hashedslasher/kaiju-ndt/plots/9-2-26/plot_20260902_162636.png

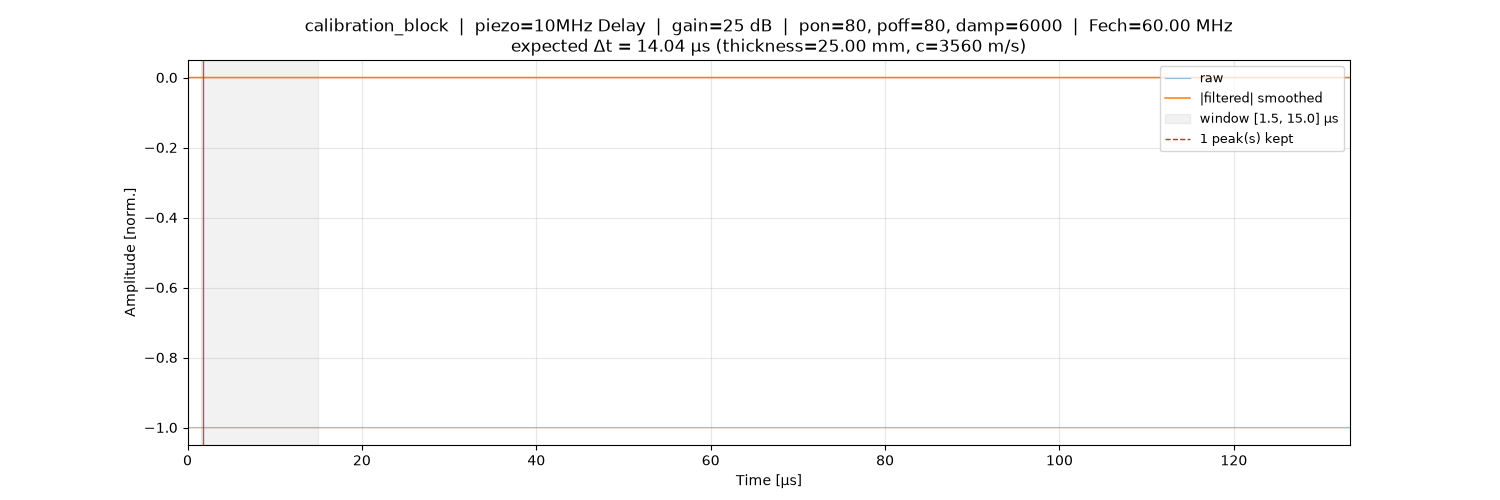
plots/9-2-26/plot_20260902_162636.png
