hashedslasher/kaiju-ndt/plots/9-3-26/plot_20260903_183738.png

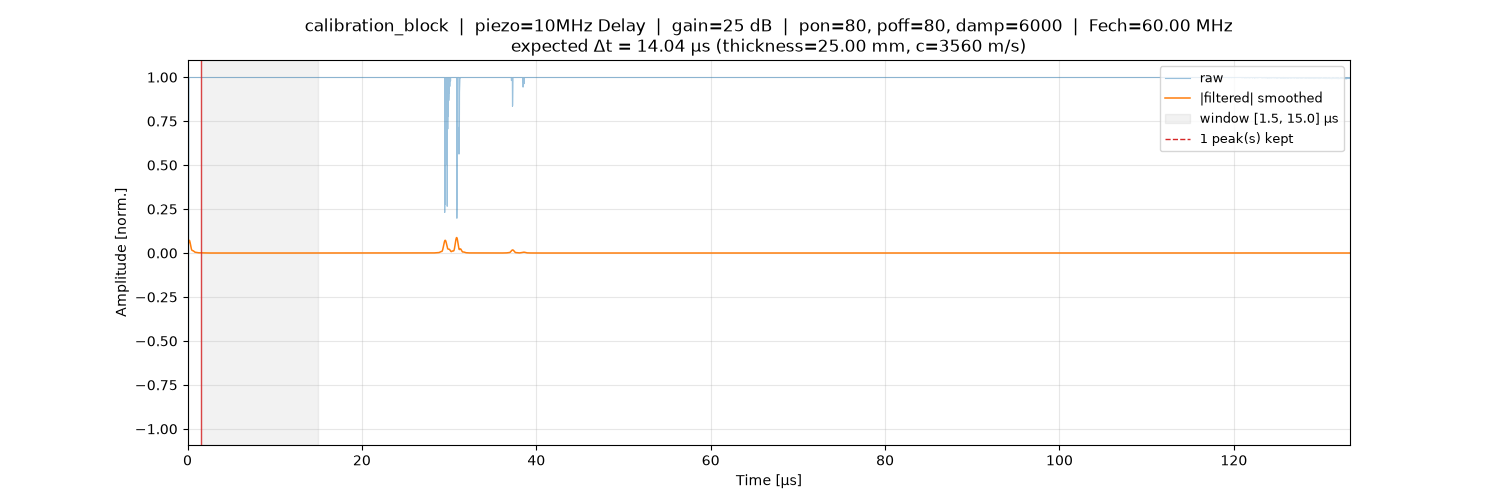
plots/9-3-26/plot_20260903_183738.png
