hashedslasher/kaiju-ndt/plots/9-3-26/plot_20260903_190933.png

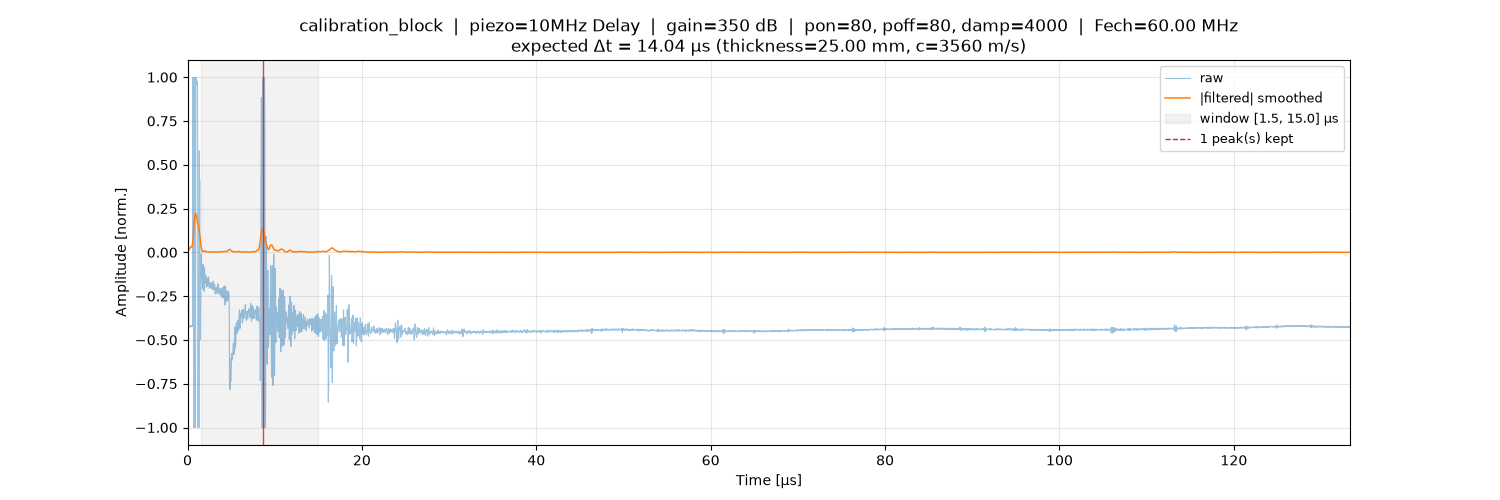
plots/9-3-26/plot_20260903_190933.png
