hashedslasher/kaiju-ndt/plots/9-3-26/plot_20260903_191829.png

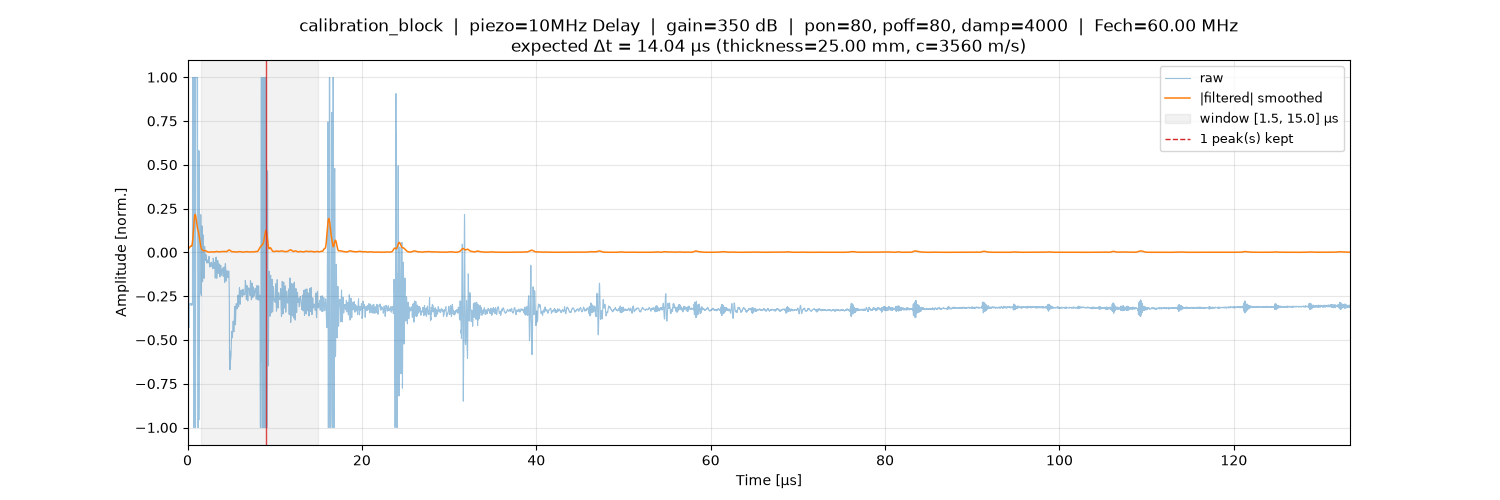
plots/9-3-26/plot_20260903_191829.png
