hashedslasher/kaiju-ndt/plots/9-3-26/plot_20260903_192204.png

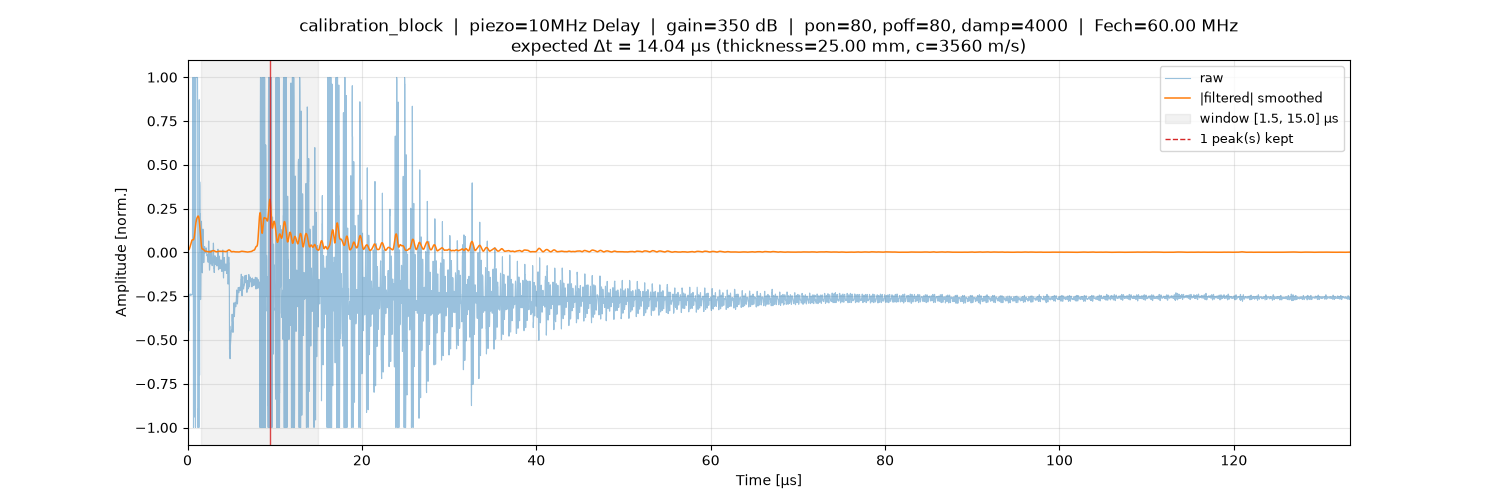
plots/9-3-26/plot_20260903_192204.png
