hashedslasher/kaiju-ndt/plots/9-4-26/plot_20260904_101053.png

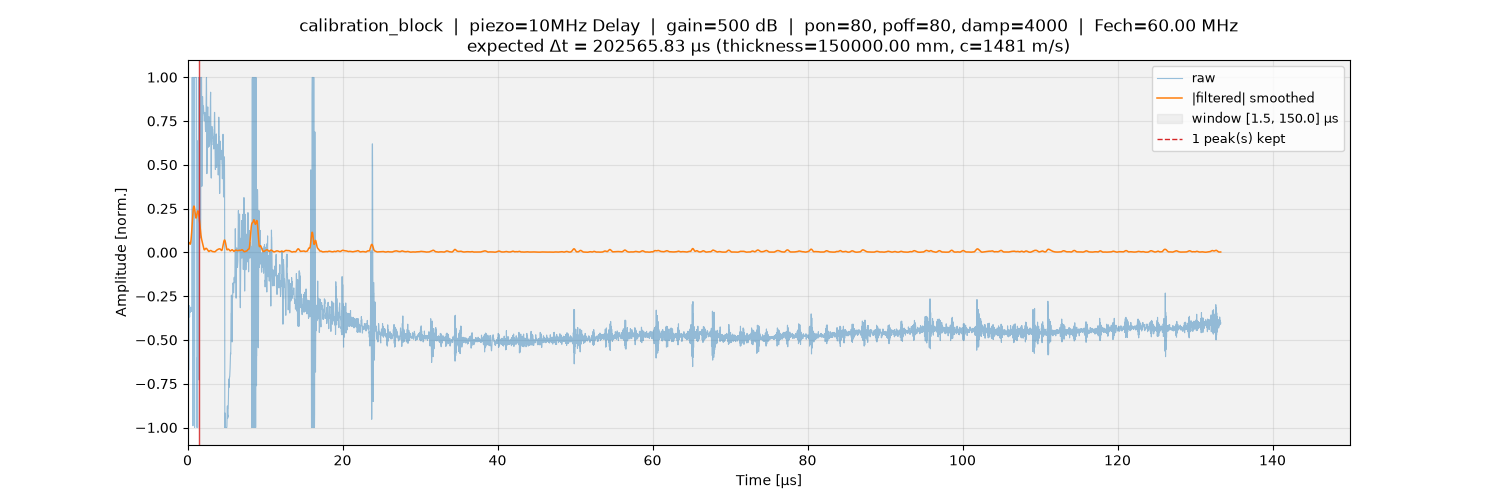
plots/9-4-26/plot_20260904_101053.png
