hashedslasher/kaiju-ndt/plots/9-4-26/plot_20260904_101120.png

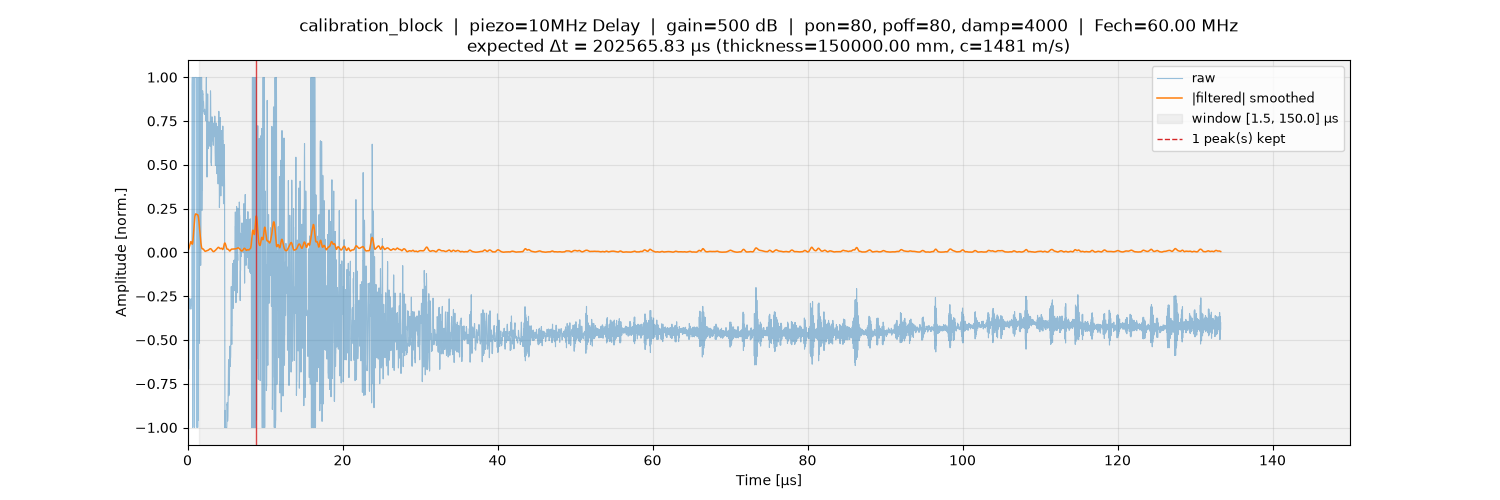
plots/9-4-26/plot_20260904_101120.png
