hashedslasher/kaiju-ndt/plots/9-4-26/plot_20260904_101206.png

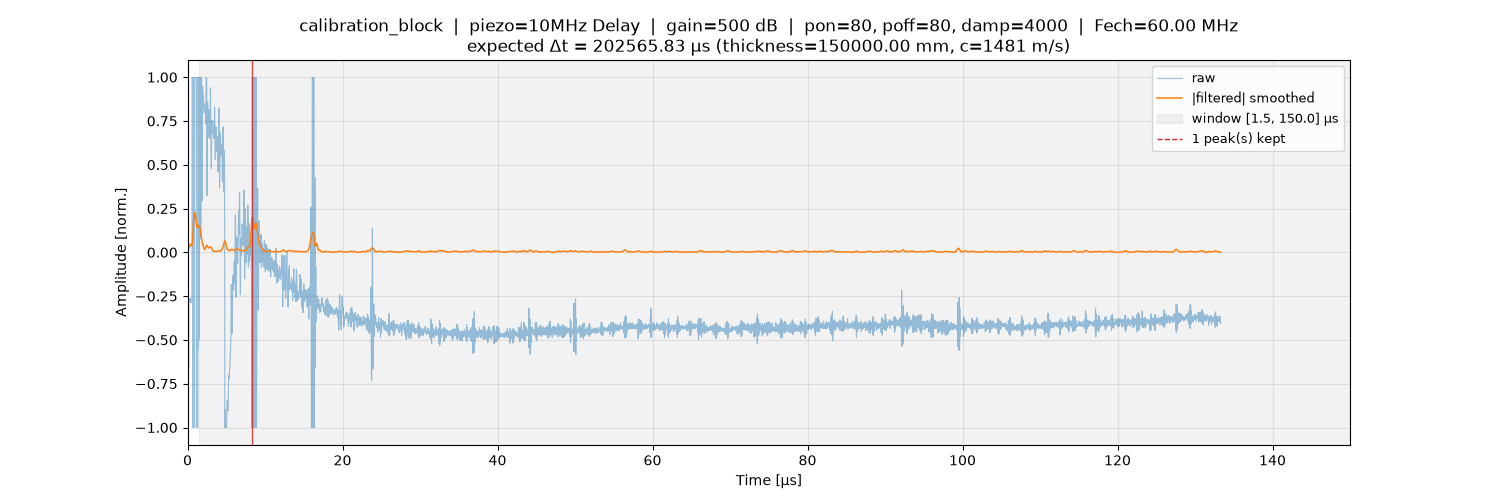
plots/9-4-26/plot_20260904_101206.png
