hashedslasher/kaiju-ndt/plots/9-4-26/plot_20260904_121708.png

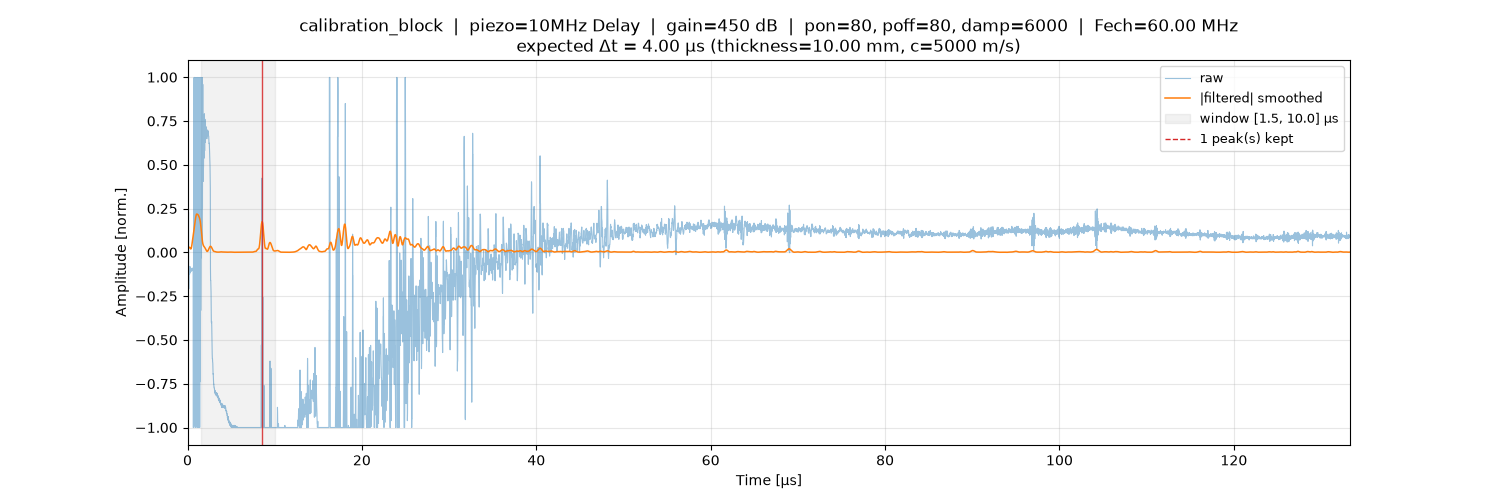
plots/9-4-26/plot_20260904_121708.png
