hashedslasher/kaiju-ndt/plots/9-4-26/plot_20260904_133635.png

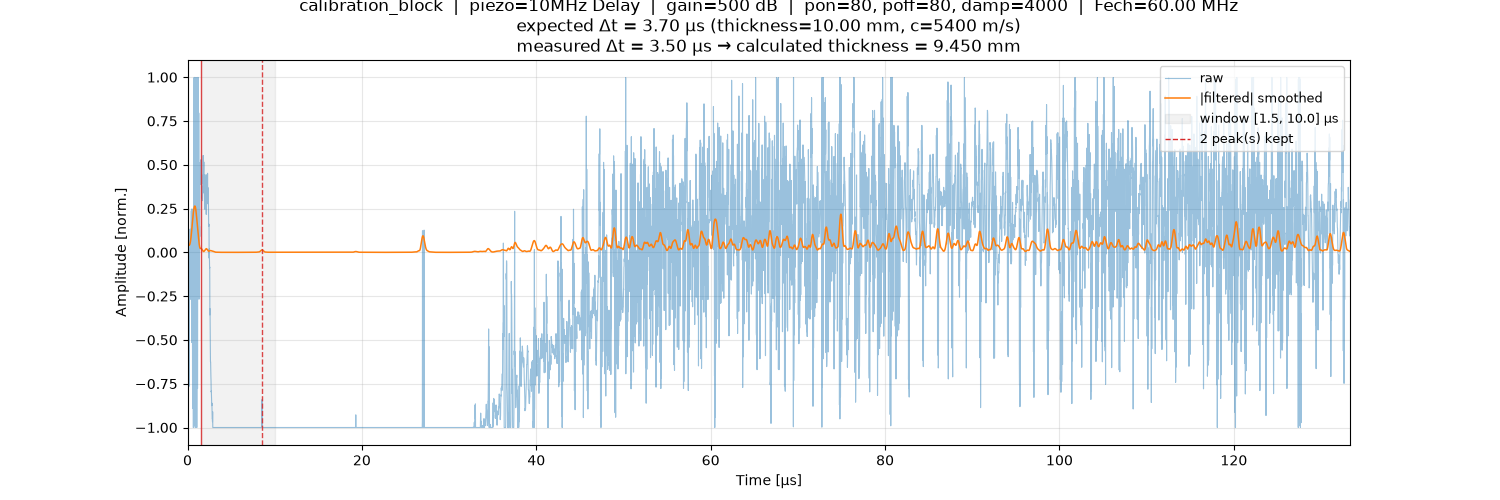
plots/9-4-26/plot_20260904_133635.png
