hashedslasher/kaiju-ndt/plots/9-4-26/plot_20260904_142144.png

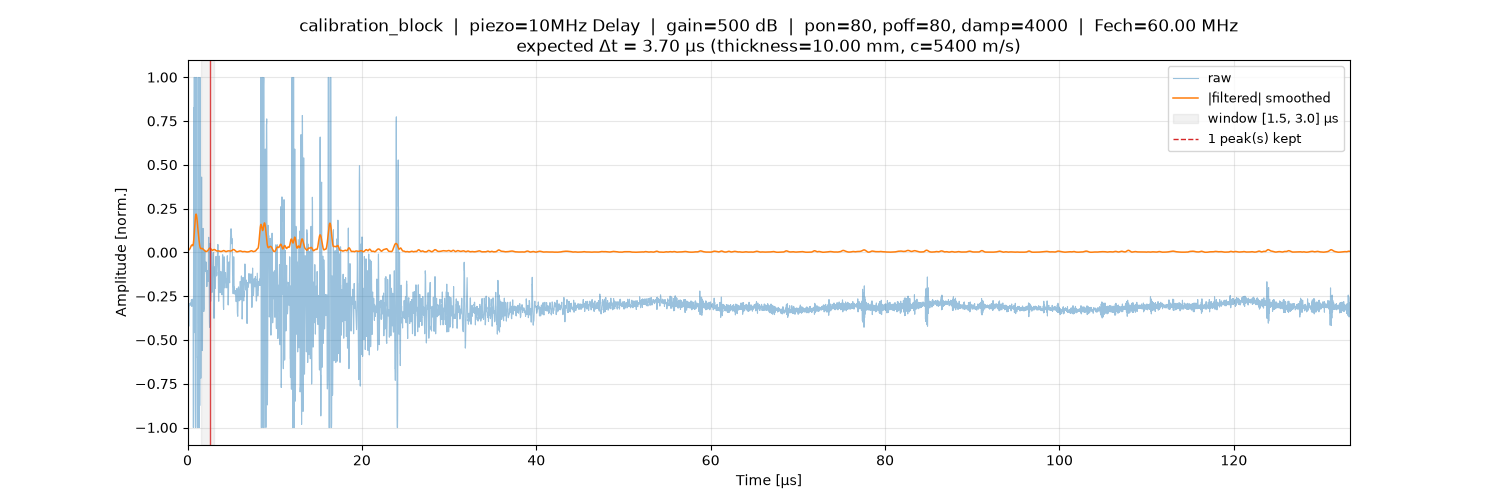
plots/9-4-26/plot_20260904_142144.png
