hashedslasher/kaiju-ndt/plots/9-4-26/plot_20260904_144540.png

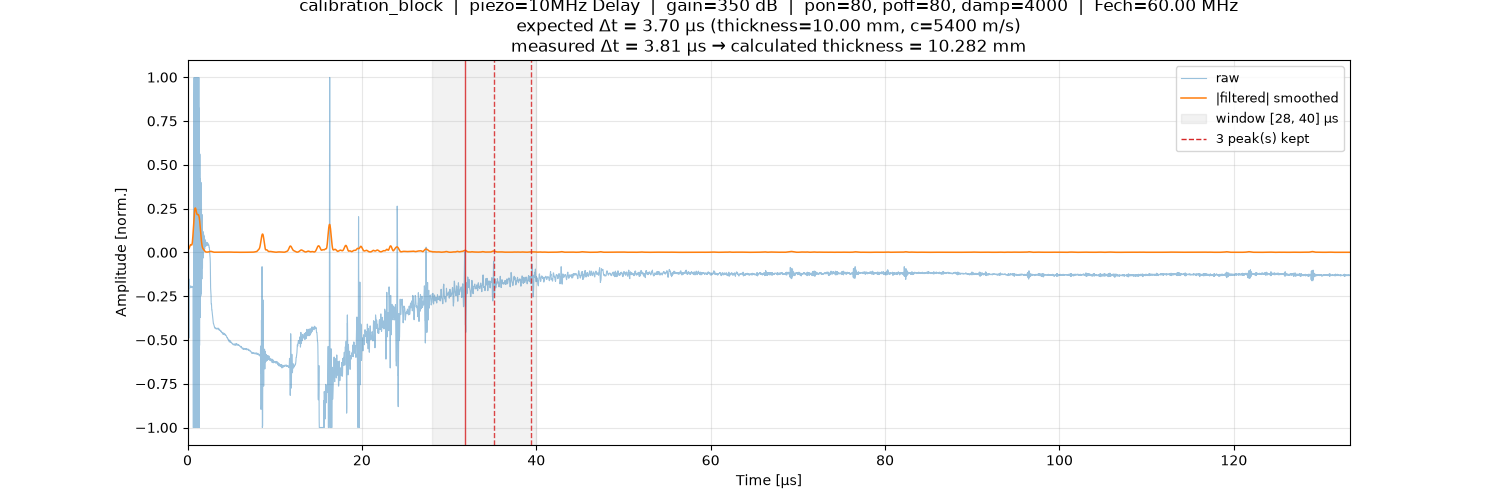
plots/9-4-26/plot_20260904_144540.png
