hashedslasher/kaiju-ndt/parts/mpcnc-primo/bolts/parts.png

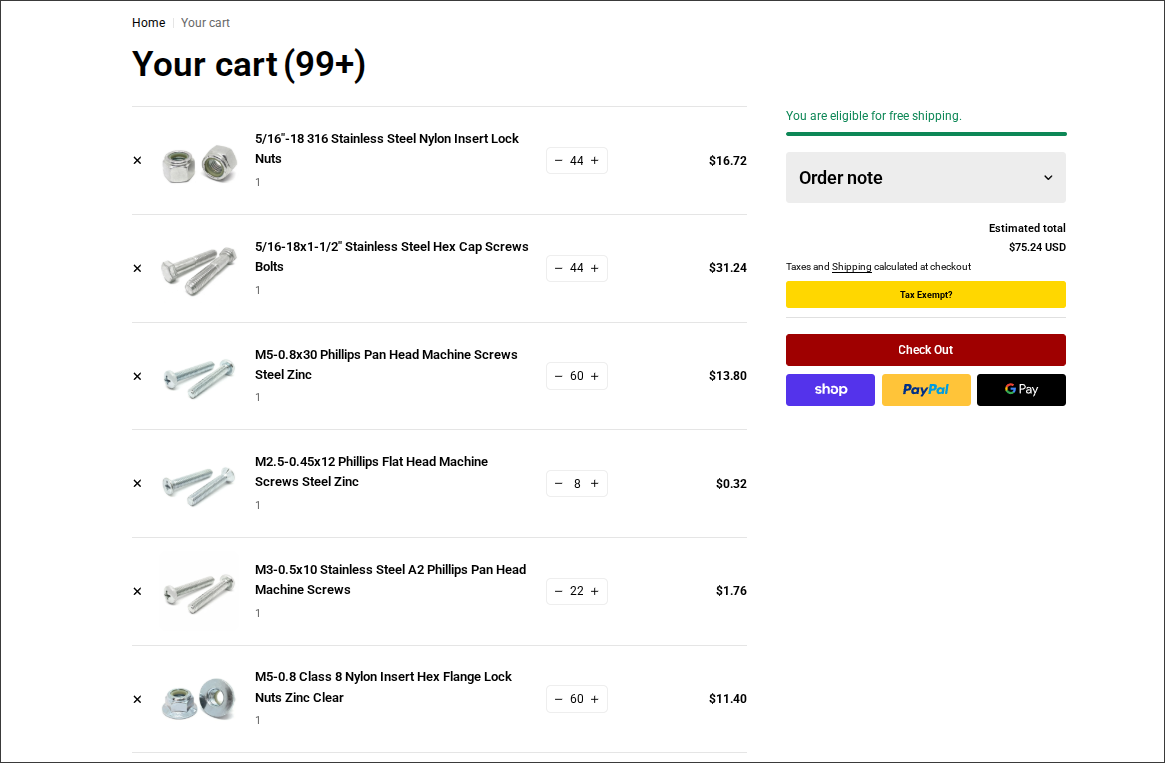
parts/mpcnc-primo/bolts/parts.png
