hashedslasher/kaiju-ndt/parts/mpcnc-primo/23-5_c-stl/color-a/wire-darryl.STL

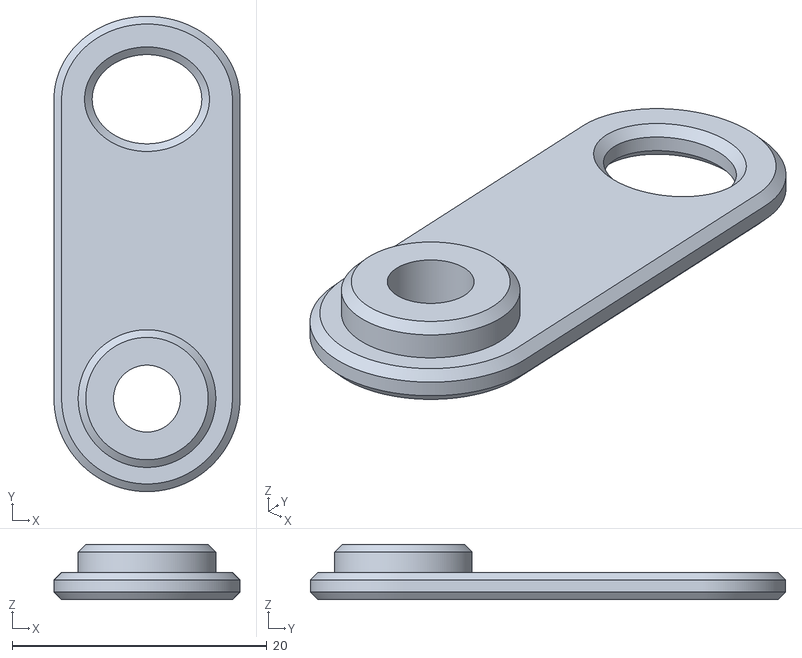
[picture p46: CAD file, 2026-09-16]
parts/mpcnc-primo/23-5_c-stl/color-a/wire-darryl.STL
14.6 x 37.3 x 4.35
