hashedslasher/kaiju-ndt/parts/mpcnc-primo/23-5_c-stl/color-a/z-coupler.STL

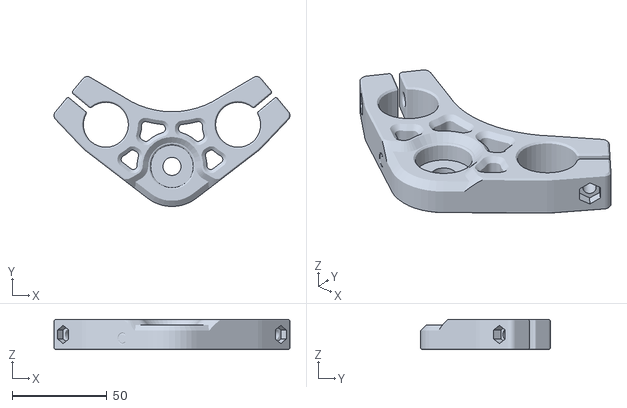
[picture p48: CAD file, 2026-09-16]
parts/mpcnc-primo/23-5_c-stl/color-a/z-coupler.STL
124.3 x 68.4 x 16.0
