hashedslasher/kaiju-ndt/parts/mpcnc-primo/23-5_c-stl/color-a/upper-tool-plate.STL

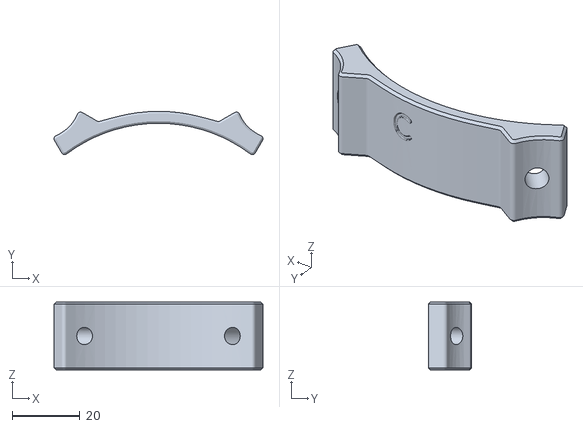
[picture p49: CAD file, 2026-09-16]
parts/mpcnc-primo/23-5_c-stl/color-a/upper-tool-plate.STL
61.7 x 12.8 x 20.0
