hashedslasher/kaiju-ndt/parts/mpcnc-primo/23-5_c-stl/color-a/core-clamp-y.STL

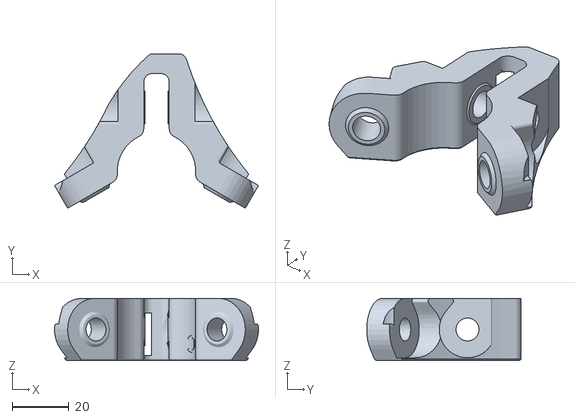
[picture p50: CAD file, 2026-09-16]
parts/mpcnc-primo/23-5_c-stl/color-a/core-clamp-y.STL
72.2 x 54.7 x 22.0
