hashedslasher/kaiju-ndt/parts/mpcnc-primo/23-5_c-stl/color-a/stop-block.STL

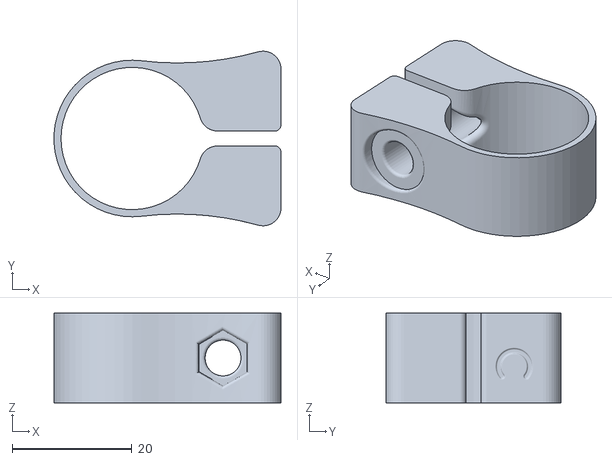
[picture p51: CAD file, 2026-09-16]
parts/mpcnc-primo/23-5_c-stl/color-a/stop-block.STL
38.0 x 29.2 x 15.0
