hashedslasher/kaiju-ndt/app/src/mainwindow.h

#ifndef MAINWINDOW_H
#define MAINWINDOW_H

#include <QMainWindow>
#include "../external/qcustomplot.h"

class MainWindow : public QMainWindow
{
    Q_OBJECT

public:
    MainWindow(QWidget *parent = nullptr);
    ~MainWindow();

private:
    QCustomPlot *customPlot;
};

#endif // MAINWINDOW_H
